kinasmith/CompostSensor/v2/Arduino/sensor-therm_moteino_dht22/jeelib-sleepy.cpp

#include "jeelib-sleepy.h"
#include <avr/sleep.h>
#include <util/atomic.h>

// flag bits sent to the receiver
#define MODE_CHANGE 0x80    // a pin mode was changed
#define DIG_CHANGE  0x40    // a digital output was changed
#define PWM_CHANGE  0x30    // an analog (pwm) value was changed on port 2..3
#define ANA_MASK    0x0F    // an analog read was requested on port 1..4


// ISR(WDT_vect) { Sleepy::watchdogEvent(); }

static volatile byte watchdogCounter;

void Sleepy::watchdogInterrupts (char mode) {
    // correct for the fact that WDP3 is *not* in bit position 3!
    if (mode & bit(3))
        mode ^= bit(3) | bit(WDP3);
    // pre-calculate the WDTCSR value, can't do it inside the timed sequence
    // we only generate interrupts, no reset
    byte wdtcsr = mode >= 0 ? bit(WDIE) | mode : 0;
    MCUSR &= ~(1<<WDRF);
    ATOMIC_BLOCK(ATOMIC_FORCEON) {
#ifndef WDTCSR
#define WDTCSR WDTCR
#endif
        WDTCSR |= (1<<WDCE) | (1<<WDE); // timed sequence
        WDTCSR = wdtcsr;
    }
}

/// @see http://www.nongnu.org/avr-libc/user-manual/group__avr__sleep.html
void Sleepy::powerDown () {
    byte adcsraSave = ADCSRA;
    ADCSRA &= ~ bit(ADEN); // disable the ADC
    set_sleep_mode(SLEEP_MODE_PWR_DOWN);
    ATOMIC_BLOCK(ATOMIC_FORCEON) {
        sleep_enable();
        // sleep_bod_disable(); // can't use this - not in my avr-libc version!
#ifdef BODSE
        MCUCR = MCUCR | bit(BODSE) | bit(BODS); // timed sequence
        MCUCR = (MCUCR & ~ bit(BODSE)) | bit(BODS);
#endif
    }
    sleep_cpu();
    sleep_disable();
    // re-enable what we disabled
    ADCSRA = adcsraSave;
}

byte Sleepy::loseSomeTime (word msecs) {
    byte ok = 1;
    word msleft = msecs;
    // only slow down for periods longer than the watchdog granularity
    while (msleft >= 16) {
        char wdp = 0; // wdp 0..9 corresponds to roughly 16..8192 ms
        // calc wdp as log2(msleft/16), i.e. loop & inc while next value is ok
        for (word m = msleft; m >= 32; m >>= 1)
            if (++wdp >= 9)
                break;
        watchdogCounter = 0;
        watchdogInterrupts(wdp);
        powerDown();
        watchdogInterrupts(-1); // off
        // when interrupted, our best guess is that half the time has passed
        word halfms = 8 << wdp;
        msleft -= halfms;
        if (watchdogCounter == 0) {
            ok = 0; // lost some time, but got interrupted
            break;
        }
        msleft -= halfms;
    }
    // adjust the milli ticks, since we will have missed several
#if defined(__AVR_ATtiny84__) || defined(__AVR_ATtiny85__) || defined (__AVR_ATtiny44__) || defined (__AVR_ATtiny45__)
    extern volatile unsigned long millis_timer_millis;
    millis_timer_millis += msecs - msleft;
#else
    extern volatile unsigned long timer0_millis;
    timer0_millis += msecs - msleft;
#endif
    return ok; // true if we lost approx the time planned
}

void Sleepy::watchdogEvent() {
    ++watchdogCounter;
}
